infinitymdm/curta/3mf/lower_housing.3mf

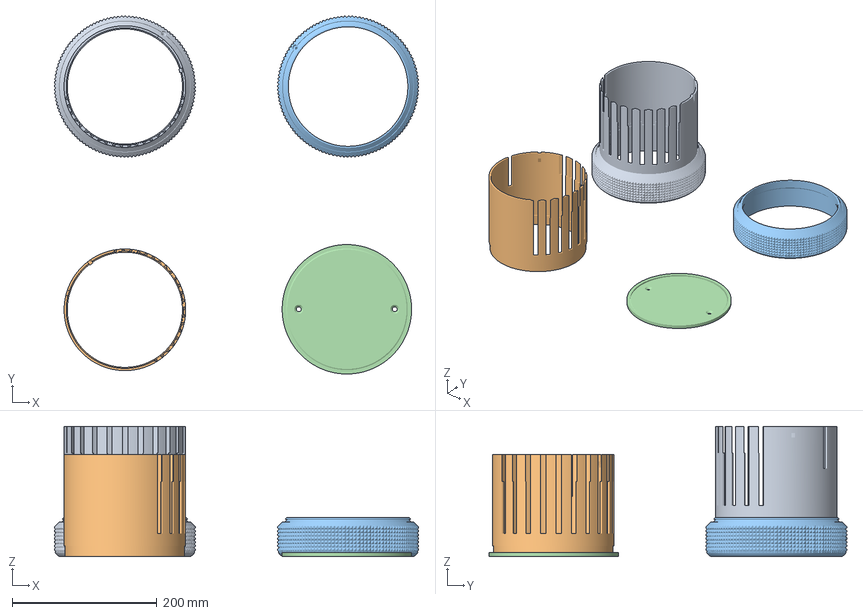
[picture p19: CAD file, 2026-08-05]
3mf/lower_housing.3mf
503.4 x 494.6 x 180.0 mm
lower_shell.stl
2120_bottom_cover.stp
