infinitymdm/curta/composites/gear_lock.stl

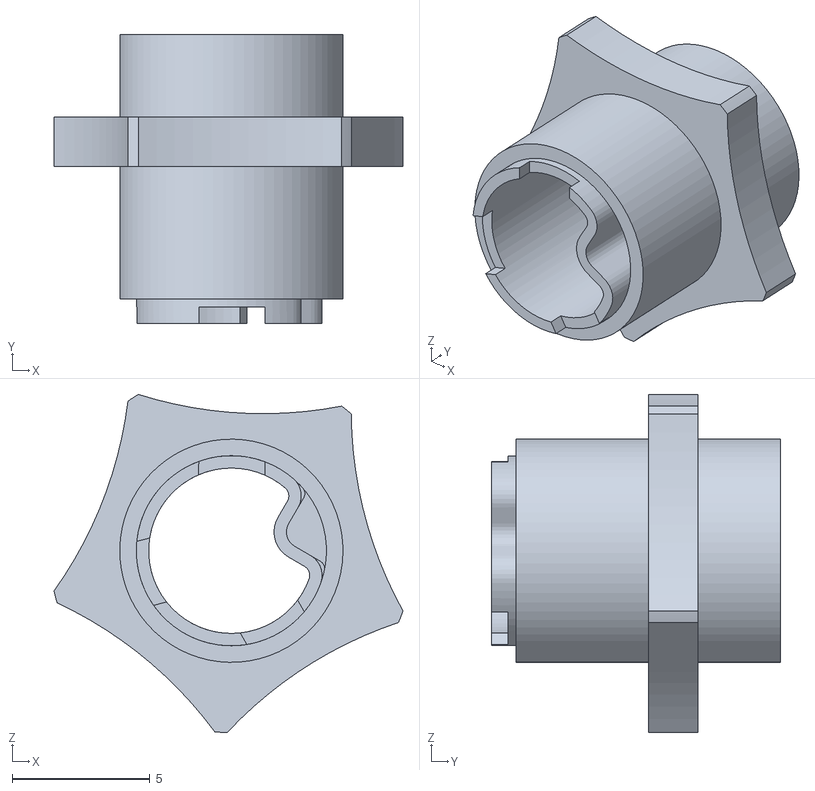
[picture p20: CAD file, 2026-07-28]
composites/gear_lock.stl
12.7 x 10.5 x 12.3
