infinitymdm/curta/custom/2130_upper_carriage_body.stl

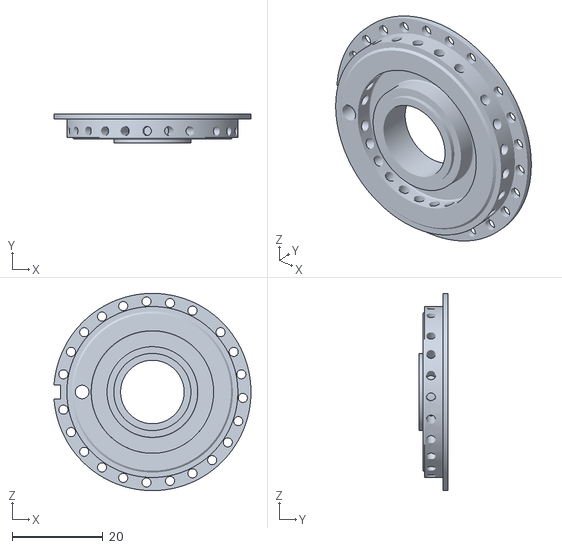
[picture p21: CAD file, 2026-08-13]
custom/2130_upper_carriage_body.stl
43.4 x 6.30 x 43.5
