infinitymdm/curta/custom/source/results_dial_-_digit_0.stl

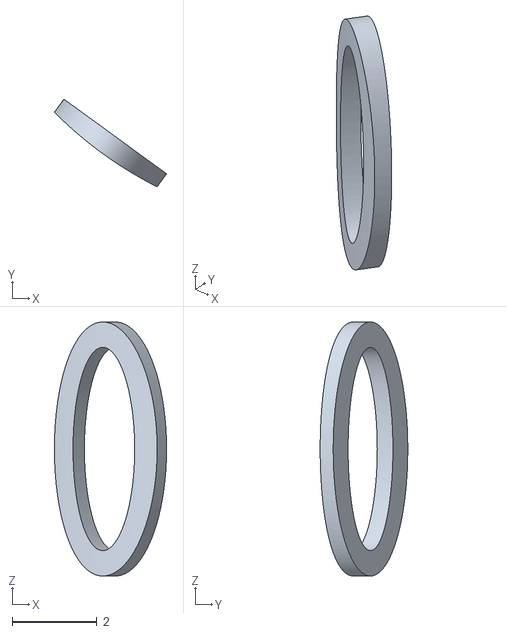
[picture p22: CAD file, 2026-08-16]
custom/source/results_dial_-_digit_0.stl
2.65 x 2.07 x 6.00
