infinitymdm/curta/3mf/reversal_switch.3mf

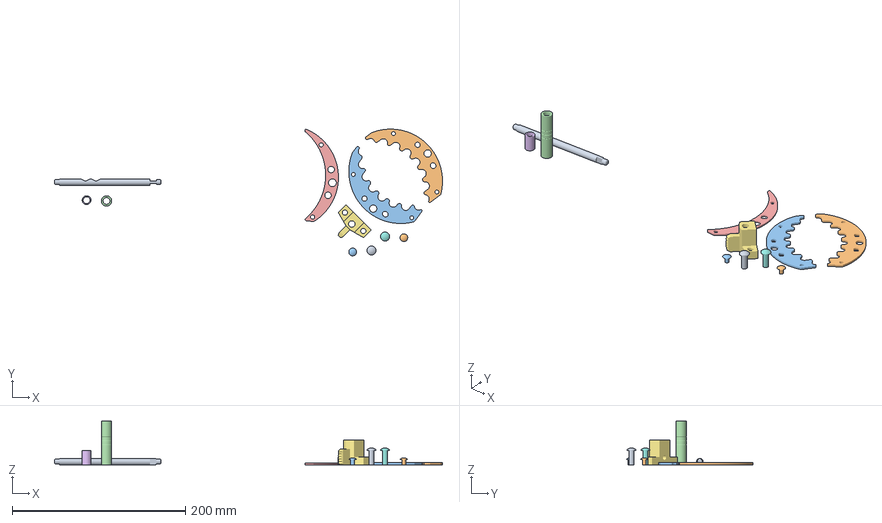
[picture p23: CAD file, 2026-08-05]
3mf/reversal_switch.3mf
448.1 x 146.4 x 50.4 mm
Halbrundniete 1,5 x 3 x 2
