infinitymdm/curta/composites/gear_step3.stl

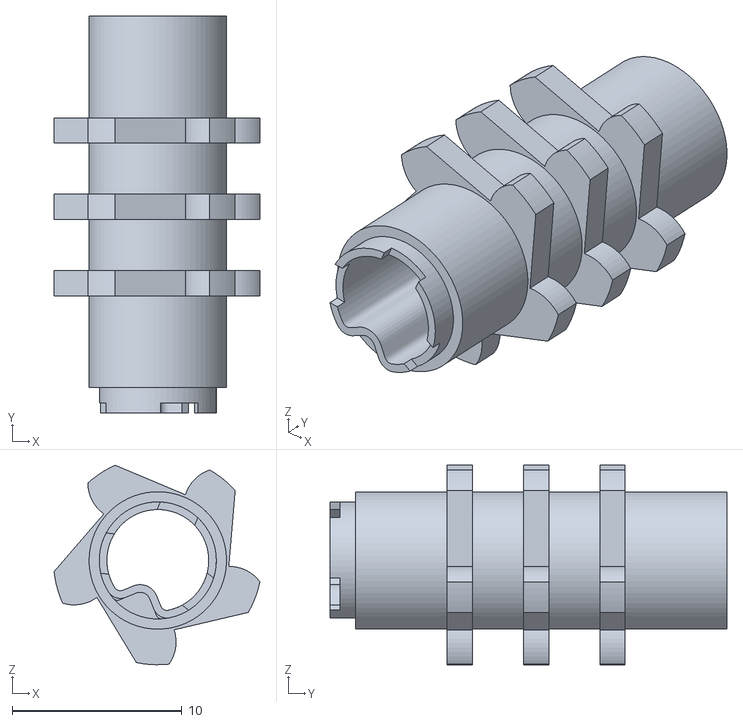
[picture p24: CAD file, 2026-07-28]
composites/gear_step3.stl
12.1 x 23.4 x 11.8
