infinitymdm/curta/custom/2120_bottom_cover.stp

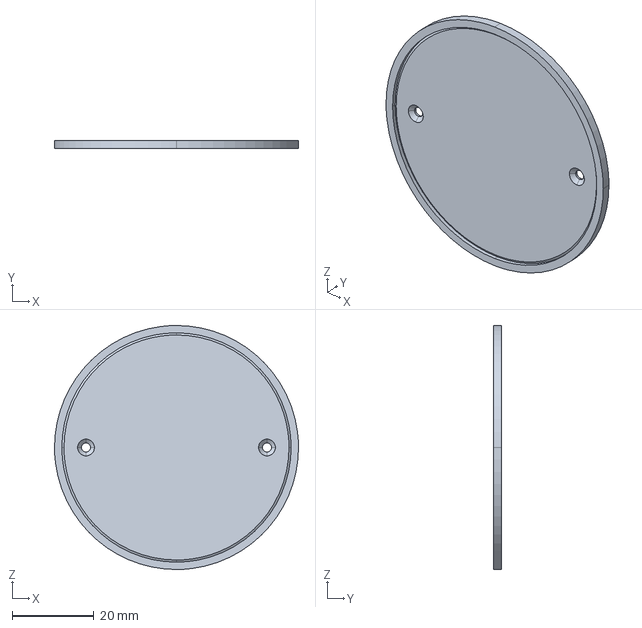
[picture p25: CAD file, 2026-08-05]
custom/2120_bottom_cover.stp
59.6 x 2.00 x 59.6 mm
