infinitymdm/curta/custom/source/results_dial_-_digit_1.stl

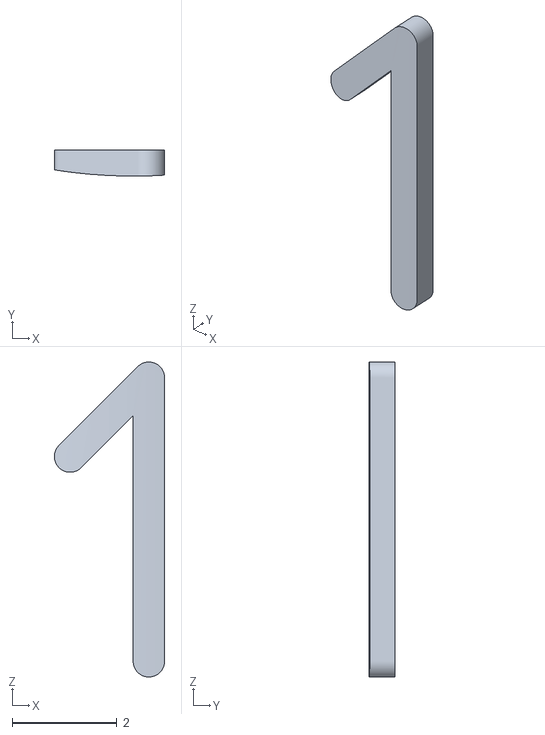
[picture p26: CAD file, 2026-08-16]
custom/source/results_dial_-_digit_1.stl
2.10 x 0.5 x 6.00
