infinitymdm/curta/composites/lower_shell.stl

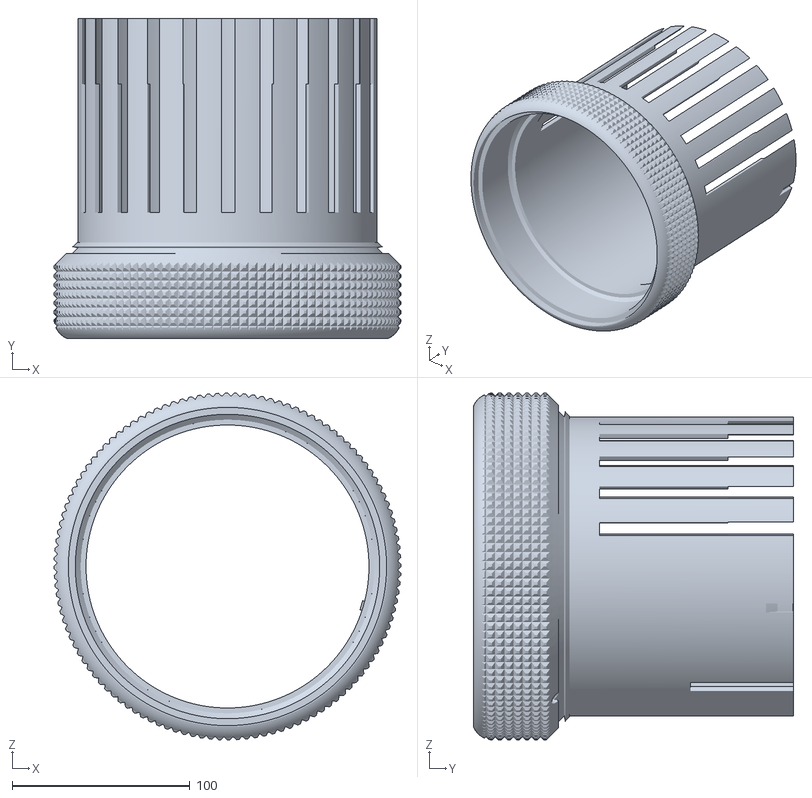
[picture p27: CAD file, 2026-07-27]
composites/lower_shell.stl
195.0 x 180.0 x 195.0
