infinitymdm/curta/custom/2063_crown_gear.stl

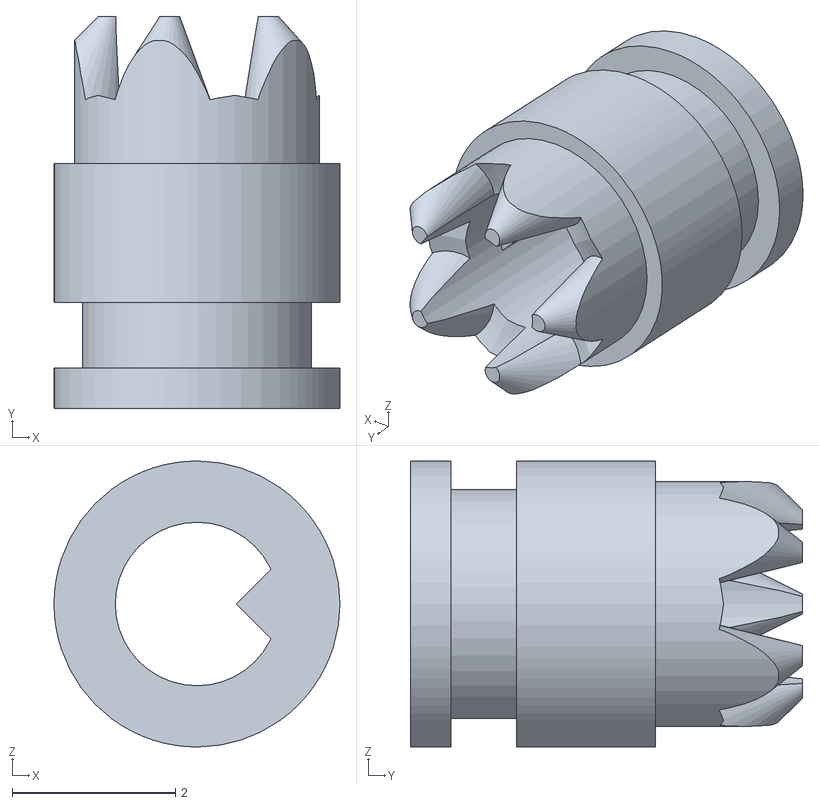
[picture p28: CAD file, 2026-07-31]
custom/2063_crown_gear.stl
3.50 x 4.80 x 3.50
