infinitymdm/curta/custom/source/2136.stl

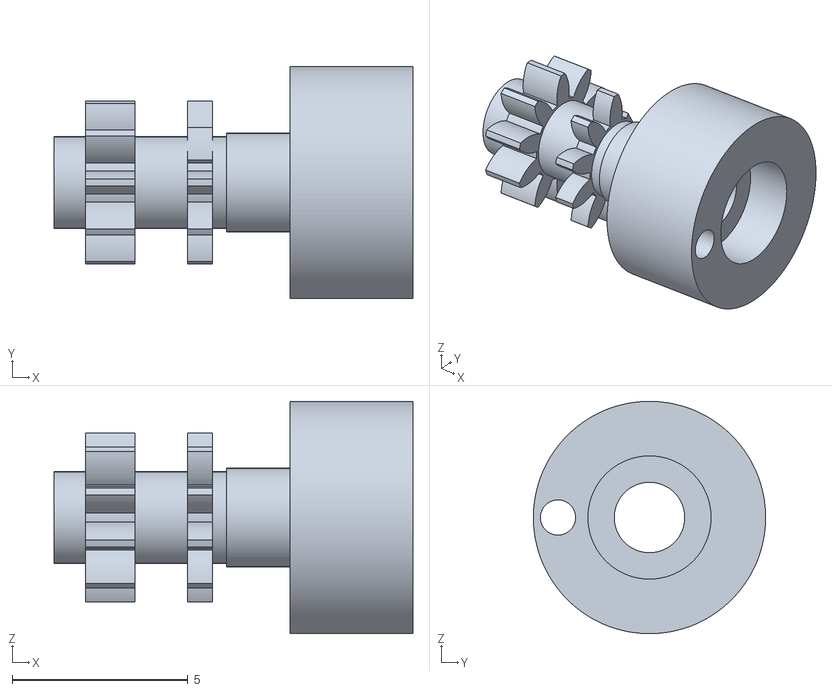
[picture p29: CAD file, 2026-08-16]
custom/source/2136.stl
10.2 x 6.60 x 6.60
