infinitymdm/curta/3mf/upper_housing.3mf

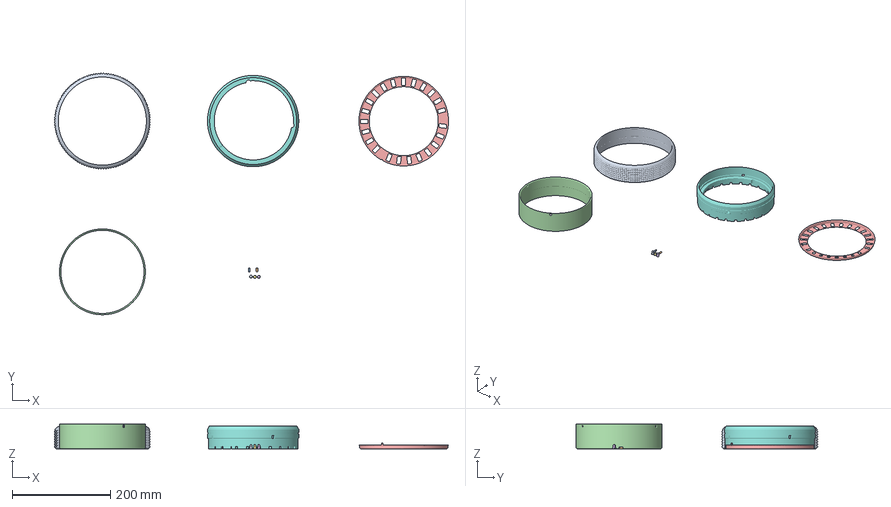
[picture p30: CAD file, 2026-08-05]
3mf/upper_housing.3mf
802.7 x 492.1 x 50.1 mm
carriage_exterior_support.stl
