infinitymdm/curta/custom/source/results_dial_-_digit_5.stl

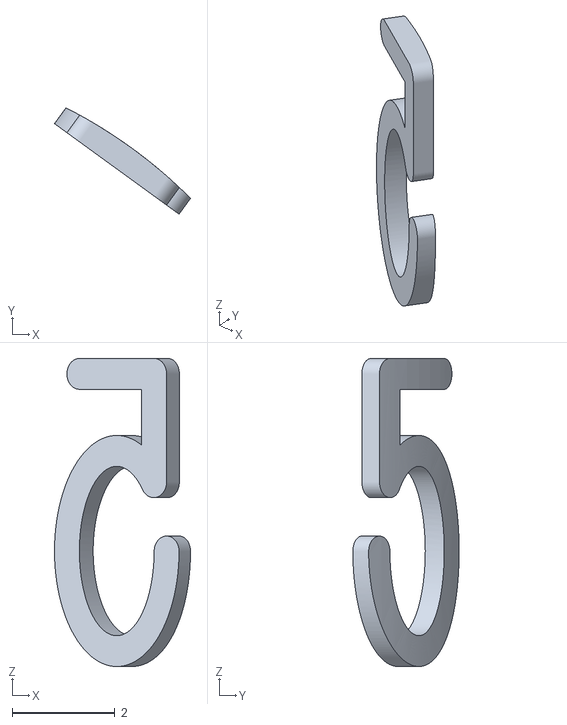
[picture p31: CAD file, 2026-08-16]
custom/source/results_dial_-_digit_5.stl
2.65 x 2.07 x 6.00
