infinitymdm/curta/composites/input_slider.stl

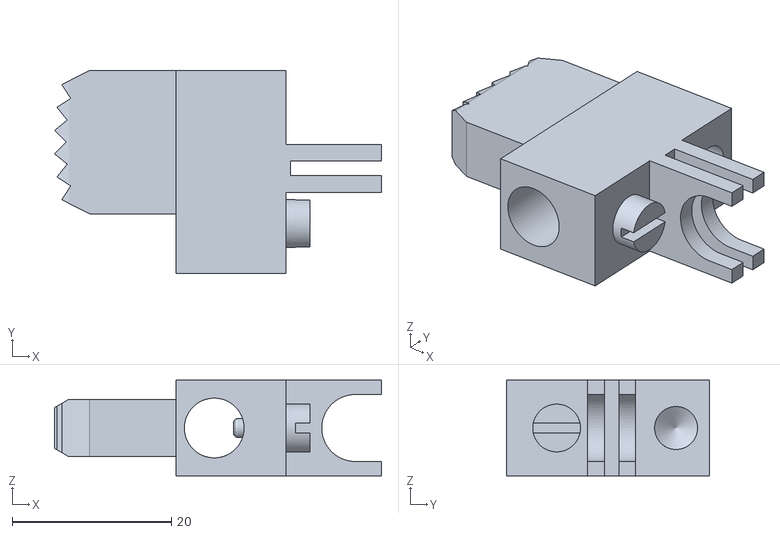
[picture p32: CAD file, 2026-07-27]
composites/input_slider.stl
41.1 x 25.5 x 12.0
