infinitymdm/curta/custom/source/results_dial_-_digit_3.stl

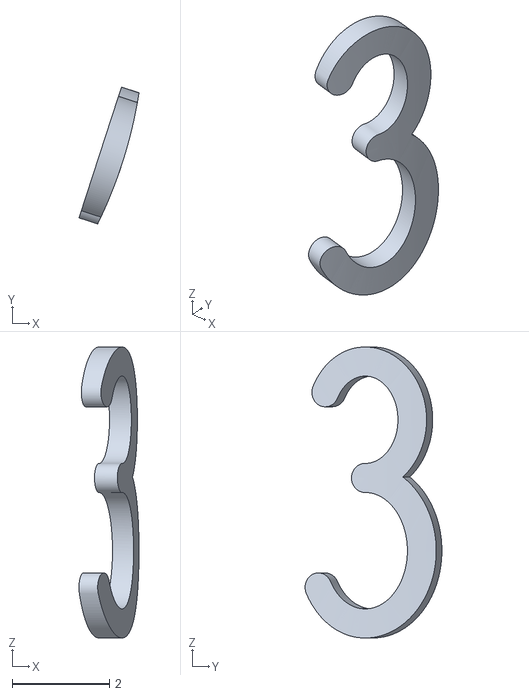
[picture p33: CAD file, 2026-08-16]
custom/source/results_dial_-_digit_3.stl
1.24 x 2.82 x 6.00
