infinitymdm/curta/3mf/zeroing_disc.3mf

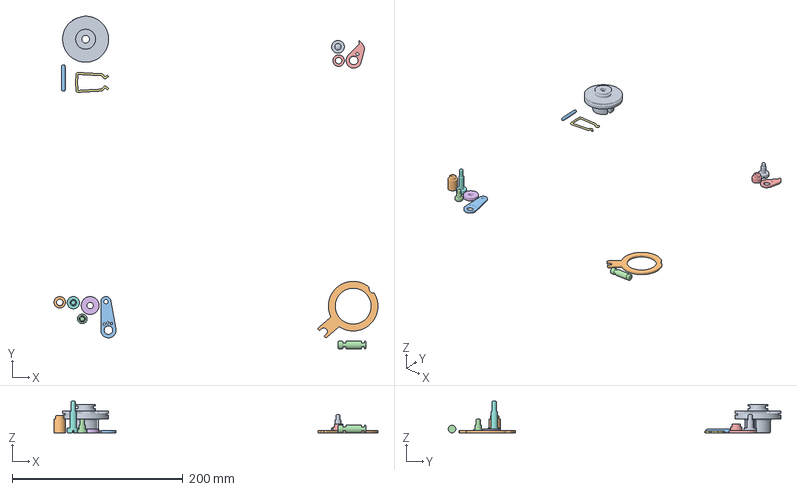
[picture p34: CAD file, 2026-07-31]
3mf/zeroing_disc.3mf
380.0 x 390.1 x 37.2 mm
lock.stl_2
lock.stl_1
