infinitymdm/curta/composites/secondary_steppers.stl

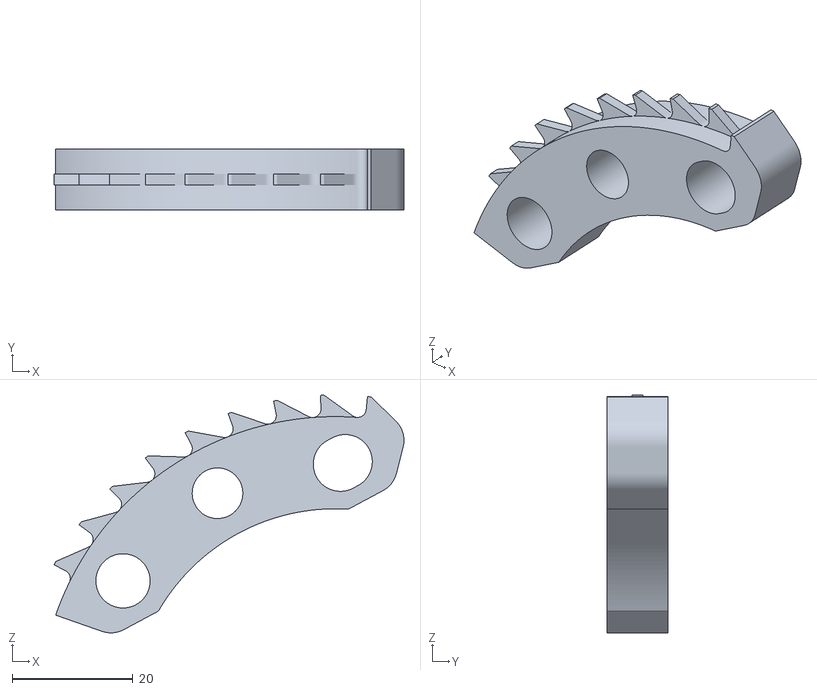
[picture p35: CAD file, 2026-07-27]
composites/secondary_steppers.stl
58.1 x 10.2 x 39.5
