infinitymdm/curta/3mf/trans_axles.3mf

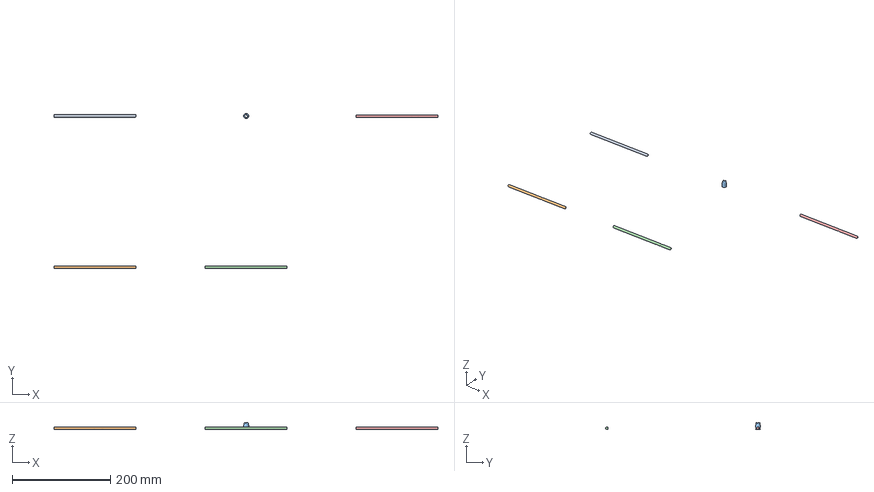
[picture p37: CAD file, 2026-07-31]
3mf/trans_axles.3mf
783.1 x 316.5 x 14.4 mm
crown_gear.stl
