infinitymdm/curta/composites/carriage_exterior_support.stl

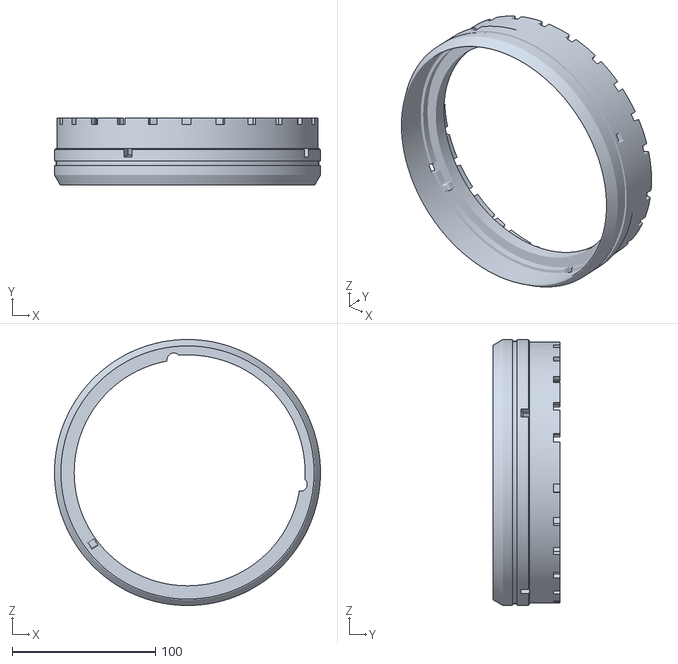
[picture p38: CAD file, 2026-07-27]
composites/carriage_exterior_support.stl
186.0 x 46.5 x 186.0
