infinitymdm/curta/custom/source/results_dial_-_digit_2.stl

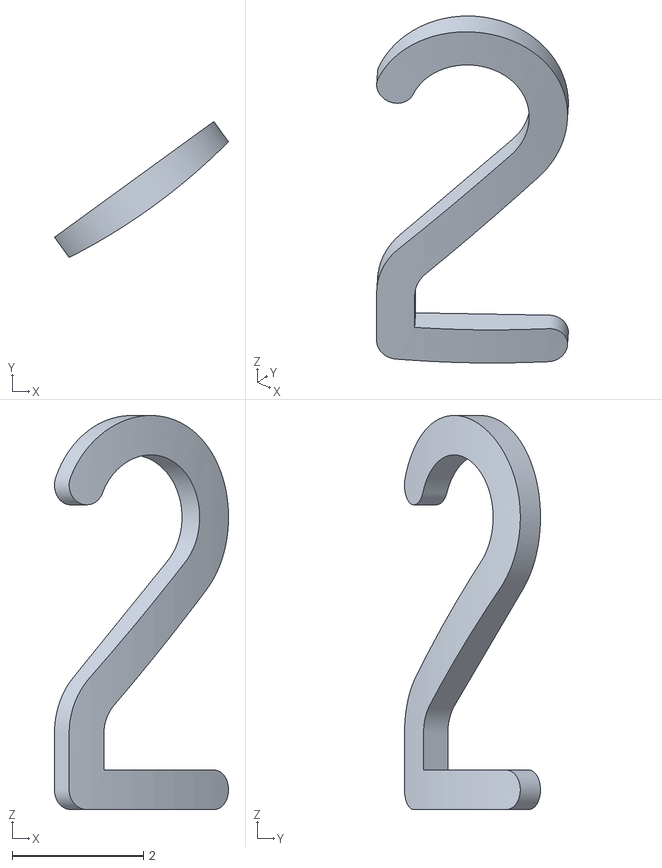
[picture p39: CAD file, 2026-08-16]
custom/source/results_dial_-_digit_2.stl
2.65 x 2.07 x 6.00
