infinitymdm/curta/3mf/tens_bell.3mf

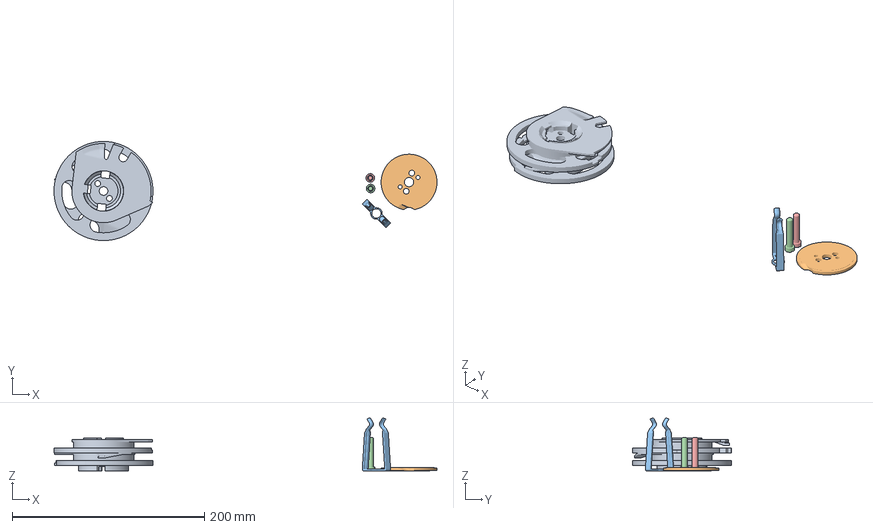
[picture p40: CAD file, 2026-07-31]
3mf/tens_bell.3mf
398.9 x 103.2 x 55.1 mm
carry_resets.stl
tens_bell_spring.stl
