infinitymdm/curta/composites/carry_resets.stl

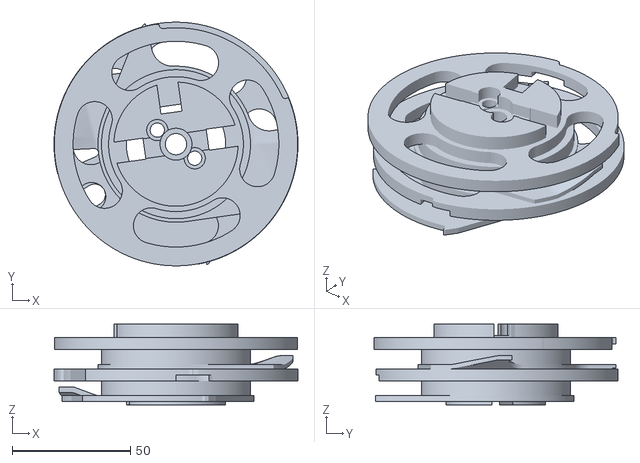
[picture p41: CAD file, 2026-07-27]
composites/carry_resets.stl
103.2 x 103.0 x 34.2
