infinitymdm/curta/3mf/trans_gears.3mf

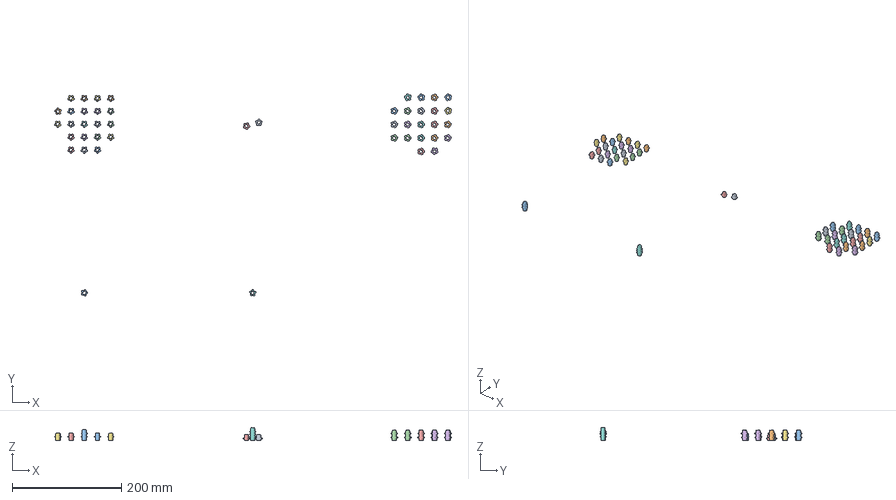
[picture p42: CAD file, 2026-07-30]
3mf/trans_gears.3mf
726.6 x 370.2 x 23.4 mm
gear_lock.stl x 2
gear_step.stl x 21
gear_step_lock.stl x 21
gear_step3.stl
gear_step2.stl
