infinitymdm/curta/custom/source/results_dial_-_digit_4.stl

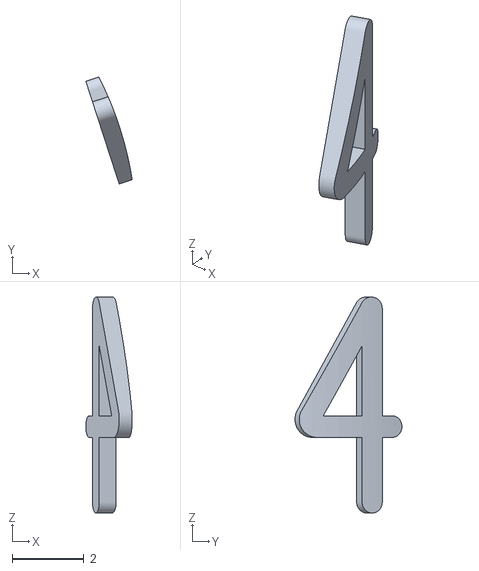
[picture p43: CAD file, 2026-08-16]
custom/source/results_dial_-_digit_4.stl
1.29 x 2.97 x 6.00
