infinitymdm/curta/3mf/step_drum.3mf

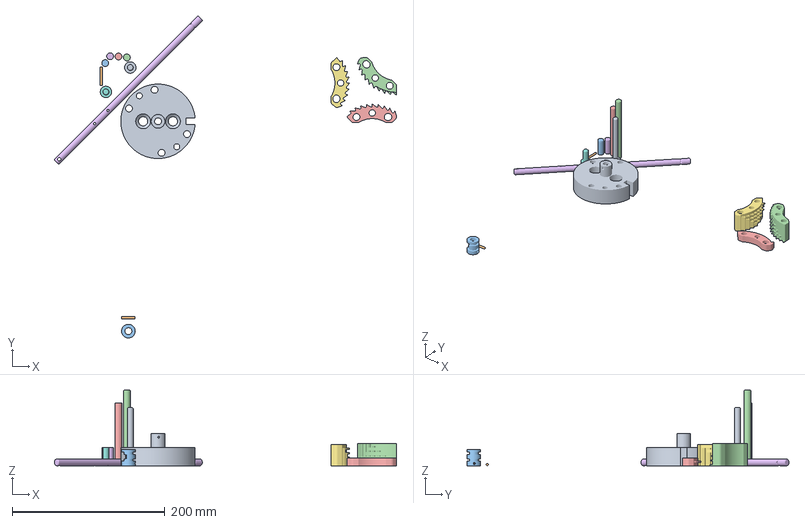
[picture p44: CAD file, 2026-07-30]
3mf/step_drum.3mf
448.4 x 421.8 x 99.0 mm
10068_reversing_ring.stl
main_lower_steppers.stl
secondary_steppers.stl
main_upper_steppers.stl
