infinitymdm/curta/3mf/frame.3mf

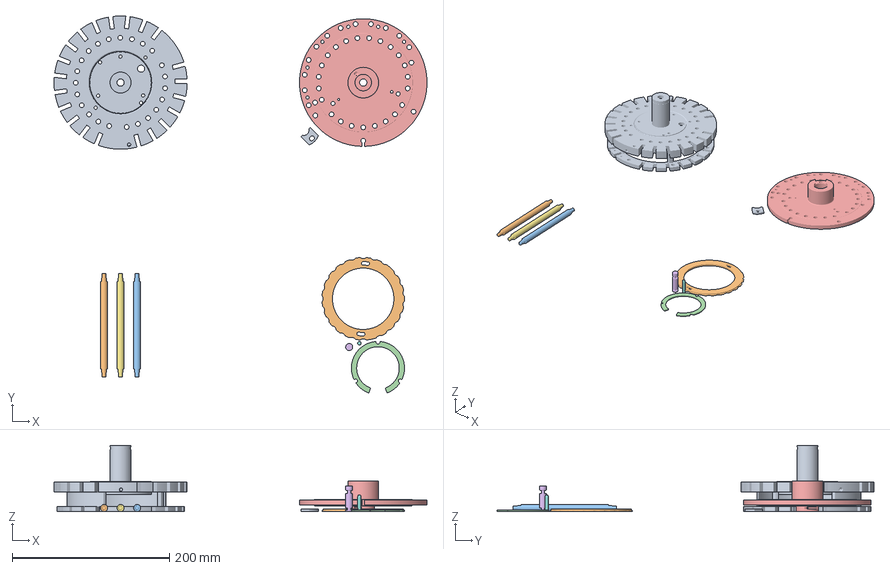
[picture p45: CAD file, 2026-07-28]
3mf/frame.3mf
474.0 x 479.1 x 84.0 mm
